jaronbrown/SDR_Receiver_Design/spice/Differential_Amp_test.asc

C1: cap; 270p
C2: cap; 37.6n
C3: cap; 37.6n
R5: res; 5.1k
R6: res; 52
R7: res; 52
U1: ADA4805
V1: voltage; SINE(2.25 10u {FREQ}); Rser=50
V2: voltage; 2.25
V3: voltage; SINE(2.25 10u {FREQ} 0 0 180); Rser=50
V4: voltage; 4.5
V5: voltage; 2.25
Named nets: +4.5, 0, 00, 11, Vout, IF, +2.25
.param C_Sample=.0155u
.meas AC V-find FIND V(Vout) AT 48k
.param FREQ=48k
.param SW_time=1/FREQ
;.ac dec 10000 1k 60Meg
Without filter capacitor: 
v-find: v(vout)=(-62.9407dB,111.894°) at 48000
With 27p capacitor:
v-find: v(vout)=(-65.1172dB,106.836°) at 48000
.noise V(Vout) V2 dec 100 1k 60Meg
