jaronbrown/SDR_Receiver_Design/spice/AM_Mixer.asc

R1: res; 50
R3: res; 10k
R4: res; 10k
S1: sw; MYSW
V1: voltage; SINE(0 1 9Meg 0 0); Rser=50
V2: voltage; SINE(4.5 0.01m 1.7Meg 0 0); Rser=50
V3: voltage; 4.5; Rser=50
V4: voltage; SINE(2.25 0.01m 1.7Meg 0 0); Rser=50
Named nets: 0, V_LO, 4.5V, V_RF, Vin, 2.25V, V_test
.tran 0 10u
.model MYSW SW(Vt=0.5 Vh=0 Ron=1 Roff=100G)
.meas vout_max max V(vout)
.meas vout_min min V(vout)
.meas vout_vpp param vout_max-vout_min
.meas vin_max max V(vin)
.meas vin_min min V(vin)
.meas vin_vpp param vin_max-vin_min
.meas amp_gain param -vout_vpp/vin_vpp
.meas vrf_max max V(v_rf)
.meas vrf_min min V(v_rf)
.meas vrf_vpp param vrf_max-vrf_min
.meas system_gain param -vout_vpp/vrf_vpp
.meas mixer_gain param vin_vpp/vrf_vpp
Figure out what
capacitor value
(is it 2x the value
thanks to switch)
10.7MHz Ceramic Filter
Mixer
Find exact characteristics of switch (use same analog multiplexor)
