jaronbrown/SDR_Receiver_Design/spice/BPF_monte_carlo.asc

C1: cap; 1µ
C2: cap; 1µ
C3: cap; 1µ
C9: cap; {150p*(1+tol1)}
C10: cap; {330p*(1+tol5)}
C11: cap; {150p*(1+tol3)}
C12: cap; 0.1µ
C13: cap; {470p*(1+tol1)}
C14: cap; {470p*(1+tol5)}
C15: cap; {470p*(1+tol3)}
C16: cap; 0.1µ
C17: cap; {6.8n*(1+tol1)}
C18: cap; {2.2n*(1+tol5)}
C19: cap; {6.8n*(1+tol3)}
C20: cap; 0.1µ
L7: ind; {390n*(1+tol2)}
L8: ind; {180n*(1+tol6)}
L9: ind; {390n*(1+tol4)}
L10: ind; {620n*(1+tol2)}
L11: ind; {560n*(1+tol6)}
L12: ind; {620n*(1+tol4)}
L13: ind; {2.7µ*(1+tol2)}
L14: ind; {9.1µ*(1+tol6)}
L15: ind; {2.7µ*(1+tol4)}
R1: res; 50
R2: res; 10k
R3: res; 50
R4: res; 10k
R5: res; 50
R6: res; 2
R13: res; 10k
R14: res; 10k
R15: res; 10k
R16: res; 50
R17: res; 10k
R18: res; 10k
R19: res; 10k
R20: res; 50
R21: res; 10k
V7: voltage; ""; AC 1u
V8: voltage; 4.5
V9: voltage; ""; AC 1u
V10: voltage; 4.5
V11: voltage; ""; AC 1u
V12: voltage; 4.5
Named nets: VRF1, 0, Butter-High, VRF2, Butter-LOW, AM, VRF3
Quick Butterworth BPF 16-30
Quick Butterworth BPF 5-16
Quick Butterworth BPF AM
.ac dec 1k 10k 100Meg
.param tol1=gauss(0.04) tol2=gauss(.04) tol3=gauss(0.04) tol4=gauss(.04) tol5=gauss(0.04) tol6=gauss(.04)
.step param N 1 300 1
