jaronbrown/SDR_Receiver_Design/spice/BPF_noise_analysis.asc

C1: cap; 150p
C2: cap; 330p
C3: cap; 150p
C4: cap; 0.1µ
C5: cap; 470p
C6: cap; 470p
C7: cap; 470p
C8: cap; 0.1µ
C9: cap; 6.8n
C10: cap; 2.2n
C11: cap; 6.8n
C12: cap; 0.1µ
C13: cap; 1µ
C14: cap; 1µ
C15: cap; 1µ
L1: ind; 390n
L2: ind; 180n
L3: ind; 390n
L4: ind; 620n
L5: ind; 560n
L6: ind; 620n
L7: ind; 2.7µ
L8: ind; 9.1µ
L9: ind; 2.7µ
R1: res; 50
R2: res; 50
R3: res; 50
R4: res; 10k
R5: res; 10k
R6: res; 10k
R7: res; 10k
R8: res; 10k
R9: res; 10k
R10: res; 10k
R11: res; 10k
R12: res; 10k
R13: res; 50
R14: res; 50
R15: res; 2
V1: voltage; ""; AC 1u
V2: voltage; 4.5
V3: voltage; ""; AC 1u
V4: voltage; 4.5
V5: voltage; ""; AC 1u
V6: voltage; 4.5
Named nets: VRF1, 0, Butter-High, VRF2, Butter-LOW, AM, VRF3
Quick Butterworth BPF 16-30
Quick Butterworth BPF 5-16
Quick Butterworth BPF AM
;.noise V(Butter-LOW) V1 dec 1k 10k 100Meg
.noise V(Butter-High) V3 dec 1k 10k 100Meg
;.noise V(AM) V5 dec 1k 10k 100Meg
