jaronbrown/SDR_Receiver_Design/spice/ensemble_BPF_Comparison.asc

C1: cap; 1µ
C2: cap; 1µ
C3: cap; 1µ
C9: cap; 150p
C10: cap; 330p
C11: cap; 150p
C12: cap; 0.1µ
C13: cap; 470p
C14: cap; 470p
C15: cap; 470p
C16: cap; 0.1µ
C17: cap; 6.8n
C18: cap; 2.2n
C19: cap; 6.8n
C20: cap; 0.1µ
L7: ind; 390n
L8: ind; 180n
L9: ind; 390n
L10: ind; 620n
L11: ind; 560n
L12: ind; 620n
L13: ind; 2.7µ
L14: ind; 9.1µ
L15: ind; 2.7µ
R1: res; 50
R2: res; 10k
R3: res; 50
R4: res; 10k
R5: res; 50
R6: res; 2
R13: res; 10k
R14: res; 10k
R15: res; 10k
R16: res; 50
R17: res; 10k
R18: res; 10k
R19: res; 10k
R20: res; 50
R21: res; 10k
V7: voltage; ""; AC 1u
V8: voltage; 4.5
V9: voltage; ""; AC 1u
V10: voltage; 4.5
V11: voltage; ""; AC 1u
V12: voltage; 4.5
Named nets: VRF1, 0, Butter-High, VRF2, Butter-LOW, AM, VRF3
Quick Butterworth BPF 16-30
Quick Butterworth BPF 5-16
Quick Butterworth BPF AM
.ac dec 1k 10k 100Meg
