jaronbrown/SDR_Receiver_Design/spice/HF_bandpass_Tayloe.asc

C1: cap; {C_Sample}
C2: cap; {C_Sample}
C3: cap; {C_Sample}
C4: cap; {C_Sample}
C5: cap; 0.35n
C6: cap; 0.35n
C7: cap; 470p
C8: cap; 470p
C9: cap; 470p
C10: cap; 0.1µ
L1: ind; 620n
L2: ind; 560n
L3: ind; 620n
R1: res; 0.1
R2: res; 0.1
R3: res; 1
R4: res; 1
R5: res; 5k
R6: res; 0.1
R7: res; 0.1
R8: res; 5k
R9: res; 0.1
R10: res; 0.1
R11: res; 50
S1: sw; MYSW
S2: sw; MYSW
S3: sw; MYSW
S4: sw; MYSW
U1: ADA4805
U2: ADA4805
V1: voltage; SINE(2.25 1u {RF_Freq}); AC 1; Rser=50
V2: voltage; PULSE(0 1 0 0.001p 0.001p {SW_time} {4*SW_time})
V3: voltage; PULSE(0 1 {SW_time} 0.001p 0.001p {SW_time} {4*SW_time})
V4: voltage; PULSE(0 1 {2*SW_time} 0.001p 0.001p {SW_time} {4*SW_time})
V5: voltage; PULSE(0 1 {3*SW_time} 0.001p 0.001p {SW_time} {4*SW_time})
V6: voltage; 4.5
Named nets: 0, V_0_deg, V_90_deg, V_180_deg, V_270_deg, 00, 11, 01, 10, +4.5, vout, vin, Butter-LOW
.model MYSW SW(Vt=0.9 Vh=0 Ron=1 Roff=100G)
.tran 0 6m 5.5m 10u
;.noise V(V_outQ) V3 dec 10 10 100meg
;.op
.param RF_freq=10Meg LO_freq={RF_freq - Audio_freq} LO_period={1/LO_freq} SW_time={LO_period/4}
.param C_Sample=8.2n
Signals for voltage-controlled switches 
used to simulate our multiplexer.
Power Connections
RF signal in
Multiplexer
Simulation Control
;step dec param Audio_freq 1000 10000000 1
.param Audio_freq=48000
R2 and R3 to emulate PE1NNZ
Measurement
.meas vout_max max V(vout)
.meas vout_min min V(vout)
.meas vout_vpp param vout_max-vout_min
.meas vin_max max V(vin)
.meas vin_min min V(vin)
.meas vin_vpp param vin_max-vin_min
.meas amp_gain PARAM -vout_vpp/vin_vpp
Given the resistor values for the op-amp biasing, one would expect the gain to be A = 100k/52 = 2000.
However, we see an apparent gain of A = 500 which is thanks to the average voltage being 1/4 of the
actual input voltage due to the signal average from the switching. We do in fact have a gain of 2000,
but the input to the amplifier is 1/4 what we would have expected.
Quick Butterworth BPF 5-16
