jaronbrown/SDR_Receiver_Design/spice/MOSFET_impedance_matching.asc

C1: cap; 10µ
C2: cap; 10µ
C3: cap; 10µ
C4: cap; 10µ
E1: e; 1
M1: nmos; 2N7002
M2: nmos; 2N7002
R1: res; 5k
R2: res; 50
R3: res; 1k
R4: res; 1k
R5: res; 50
R6: res; 5k
R7: res; 5k
R8: res; 50
R9: res; 5k
R10: res; 50
V1: voltage; 4.5
V2: voltage; SINE(0 .0002 10.7Meg)
Named nets: 0, v_rf, VCC, xstal_in, xstal_out, vo
;.tran 0 32m 30m 0.1m
Common Gate Amp
(what about 1/gm parallel with R2 for Rin?)
Source Follower Amp
(what about 1/gm parallel with R8 for Rout?)
xstal
Need to verify coupling caps?
Are they even necessary for xstal I/O?
What about the one from v_rf? It comes from a BPF?
Supply & Signal
.op
