jaronbrown/SDR_Receiver_Design/spice/OpAmp_impedance_matching.asc

R1: res; 47
R2: res; 68
R3: res; 4.7k
R4: res; 4k
R5: res; 50
R6: res; 1k
R7: res; 1k
R8: res; 50
R9: res; 4.7k
U1: ADA4805
U2: ADA4805
V1: voltage; 4.5
V2: voltage; SINE(2.25 10u 10.7Meg); Rser=50
V3: voltage; 2.25; AC .1m; Rser=50
Named nets: +4.5, 0, +2.25, vin, vout
Measurement
.meas vout_max max V(vout)
.meas vout_min min V(vout)
.meas vout_vpp param vout_max-vout_min
.meas vin_max max V(vin)
.meas vin_min min V(vin)
.meas vin_vpp param vin_max-vin_min
.meas amp_gain PARAM -vout_vpp/vin_vpp
.ac dec 1000 1k 15Meg
