jaronbrown/SDR_Receiver_Design/spice/Ring_mixer.asc

C1: cap; 63.4p
C2: cap; 619p
C3: cap; 97.6p
C4: cap; 402p
D1: diode; DI_1N5711
D2: diode; DI_1N5711
D3: diode; DI_1N5711
D4: diode; DI_1N5711
L1: ind2; 1µ
L2: ind2; 0.5µ
L3: ind2; 0.5µ
L4: ind2; 0.5µ
L5: ind2; 0.5µ
L6: ind2; 1µ
L7: ind; 1.5µ
L8: ind; 160n
L9: ind; 1µ
L10: ind; 240n
R2: res; 51
R3: res; 210k
U1: ADA4805
V1: voltage; 4.5; Rser=5
V2: voltage; 2.25; Rser=5
V5: voltage; SINE(0 1 100Meg 0 0); Rser=5
V6: voltage; SINE(2.25 0.00002 120Meg 0 0); Rser=5
Named nets: 0, V_RF, V_LO, V_IF, V_BPF2, 4.5V, Out
.tran 1u
*SRC=1N5711;DI_1N5711;Diodes;Si;  70.0V  15.0mA  1.00ns   Diodes Inc. -
.MODEL DI_1N5711 D  ( IS=315n RS=2.80 BV=70.0 IBV=10.0u
+ CJO=2.00p  M=0.333 N=2.03 TT=1.44n )
K1 L1 L2 L3 1
K2 L4 L5 L6 1
Ring Diode Mixer
5-52MHz Chebyshev Bandpass FIlter
Needs a good bandpass filter before the mixer to reduce images
