jaronbrown/SDR_Receiver_Design/spice/xstal_ImpedanceMatching.asc

C1: cap; 310p
C2: cap; 3p
C3: cap; 310p
C4: cap; 3p
C5: cap; 310p
C6: cap; 3p
E1: e; 0.5
R1: res; 5k
R2: res; 50
R3: res; 1k
R4: res; 1k
R5: res; 50
R6: res; 5k
R7: res; 5k
R8: res; 50
R9: res; 5k
R10: res; 50
R11: res; 50
R12: res; 5k
R13: res; 50
test1: voltage; ""; AC .0001 0
test: voltage; ""; AC .0001 0
U1: AO3400
U2: AO3400
U3: AO3400
V1: voltage; 4.5
Named nets: 0, v_rf, VCC, xstal_in, xstal_out, vo, vs_M1, vd_M1, vg_M2, vs_M2, test, out
;.tran 0 32m 30m 0.1m
Common Gate Amp
(what about 1/gm parallel with R2 for Rin?)
Cutoff between 5-10MHz??
Source Follower Amp
(what about 1/gm parallel with R8 for Rout?)
xstal
Need to verify coupling caps?
Are they even necessary for xstal I/O?
What about the one from v_rf? It comes from a BPF?
Supply & Signal
;.op
.ac dec 100 1k 100Gig
.SUBCKT AO3400 4 1 2
M1  3 1 2 2 NMOS W=998956u  L=1.0u 
M2  2 1 2 4 PMOS W=998956u  L=0.4u
R1  4 3     RTEMP 15E-3
CGS 1 2     225E-12
DBD 2 3     DBD
**************************************************************************
.MODEL  NMOS       NMOS  (LEVEL  = 3               TOX    = 2.5E-8
+ RS     = 2E-4           RD     = 0               NSUB   = 1.6E17  
+ kp     = 3E-5                   UO     = 600             THETA  = 0
+ VMAX   = 0              XJ     = 4E-7            KAPPA  = 1.1
+ ETA    = 0              TPG    = 1  
+ IS     = 0              LD     = 0                           
+ CGSO   = 0              CGDO   = 0               CGBO   = 0 
+ NFS    = 2E10         DELTA  = 0.1)
*************************************************************************
.MODEL  PMOS       PMOS (LEVEL   = 3               TOX    = 2.5E-8
+NSUB    = 2.0E16           TPG    = -1)   
*************************************************************************
.MODEL DBD D (CJO=690E-12     VJ=0.6    M=0.3
+RS=0.005 FC=0.5 IS=1E-11 TT=1.5E-8 N=1.0 BV=36 IBV=1E-4)
*************************************************************************
.MODEL RTEMP RES (TC1=6.5E-3   TC2=1E-6)
*************************************************************************
.ENDS
Gain is awful (-60dB)
Q point seems strange, perhaps the A3400 model is bad
